nonik0/NONIK0/firmware/rust/src/modes/mod.rs

use crate::{adc::Adc, tone::Tone, Display, Event, SavedSettings, Setting, NUM_CHARS};
use enum_dispatch::enum_dispatch;

#[cfg(feature = "board_v0")]
use avrxmega_hal::{
    port::{mode::*, Pin}
};

#[cfg(feature = "board_v0")]
type ExtPinInt = crate::PB1;

#[cfg(feature = "board_v0")]
pub struct ExtPin(Option<Pin<Input<AnyInput>, ExtPinInt>>);

#[cfg(feature = "board_v0")]
impl ExtPin {
    fn new(
        ext_pin: Pin<Input<AnyInput>, ExtPinInt>,
    ) -> Self {
        Self(Some(ext_pin))
    }

    #[inline(never)]
    fn set_pin_mode(&mut self, pull_up: bool) {
        if let Some(ext_pin) = self.0.take() {
            self.0 = Some(if pull_up {
                ext_pin.into_pull_up_input().forget_imode()
            } else {
                ext_pin.into_floating_input().forget_imode()
            });
        }
    }

    fn to_pull_up(&mut self) {
        self.set_pin_mode(true);
    }

    #[inline(always)]
    fn to_floating(&mut self) {
        self.set_pin_mode(false);
    }
}


mod menu;
#[cfg(not(feature = "no_nametag"))]
mod nametag;
#[cfg(not(feature = "no_i2cutils"))]
mod i2c_utils;
#[cfg(not(feature = "no_random"))]
mod random;
#[cfg(not(feature = "no_sensors"))]
mod sensors;
#[cfg(not(feature = "no_settings"))]
mod settings;
#[cfg(not(feature = "no_traffic"))]
mod traffic;
#[cfg(not(feature = "no_tunnel"))]
mod tunnel;
#[cfg(not(feature = "no_vibes"))]
mod vibes;

pub use menu::*;
#[cfg(not(feature = "no_nametag"))]
pub use nametag::*;
#[cfg(not(feature = "no_i2cutils"))]
pub use i2c_utils::*;
#[cfg(not(feature = "no_random"))]
pub use random::*;
#[cfg(not(feature = "no_sensors"))]
pub use sensors::*;
#[cfg(not(feature = "no_settings"))]
pub use settings::*;
#[cfg(not(feature = "no_traffic"))]
pub use traffic::*;
#[cfg(not(feature = "no_tunnel"))]
pub use tunnel::*;
#[cfg(not(feature = "no_vibes"))]
pub use vibes::*;

pub const NUM_MODES: usize = {
    let mut count = 1;
    #[cfg(not(feature = "no_nametag"))]
    {
        count += 1;
    }
    #[cfg(not(feature = "no_i2cutils"))]
    {
        count += 1;
    }
    #[cfg(not(feature = "no_random"))]
    {
        count += 1;
    }
    #[cfg(not(feature = "no_sensors"))]
    {
        count += 1;
    }
    #[cfg(not(feature = "no_settings"))]
    {
        count += 1;
    }
    #[cfg(not(feature = "no_traffic"))]
    {
        count += 1;
    }
    #[cfg(not(feature = "no_tunnel"))]
    {
        count += 1;
    }
    #[cfg(not(feature = "no_vibes"))]
    {
        count += 1;
    }
    count
};

pub const MODE_NAMES: [&[u8; NUM_CHARS]; NUM_MODES] = [
    b"  NONIK0",
    #[cfg(not(feature = "no_nametag"))]
    b" Nametag",
    #[cfg(not(feature = "no_i2cutils"))]
    b"I2C Util",
    #[cfg(not(feature = "no_random"))]
    b"  Random",
    #[cfg(not(feature = "no_sensors"))]
    b" Sensors",
    #[cfg(not(feature = "no_settings"))]
    b"Settings",
    #[cfg(not(feature = "no_traffic"))]
    b" Traffic",
    #[cfg(not(feature = "no_tunnel"))]
    b"  Tunnel",
    #[cfg(not(feature = "no_vibes"))]
    b"   Vibes",
];

pub struct Context {
    mode_init: bool,
    mode_index: u8,
    pub tone_enabled: bool,
    pub settings: SavedSettings,
}

impl Context {
    pub fn new(settings: SavedSettings) -> Self {
        let mut saved_index = settings.read_setting_byte(Setting::LastMode);
        if saved_index >= NUM_MODES as u8 {
            saved_index = 1;
        }
        Self {
            mode_init: false,
            mode_index: saved_index,
            tone_enabled: settings.read_setting_bool(Setting::Tone),
            settings,
        }
    }

    #[inline(always)]
    pub fn is_menu(&self) -> bool {
        self.mode_index == 0
    }

    #[inline(always)]
    pub fn need_update(&mut self) -> bool {
        let update = !self.mode_init;
        self.mode_init = true;
        update
    }

    #[allow(clippy::wrong_self_convention)]
    pub fn to_menu(&mut self) {
        self.mode_init = false;
        self.mode_index = 0;
    }

    pub fn mode_index(&self) -> usize {
        self.mode_index as usize
    }

    #[allow(clippy::wrong_self_convention)]
    pub fn to_mode(&mut self, index: usize) {
        self.mode_init = false;
        self.mode_index = index as u8;
        self.settings
            .save_setting_byte(Setting::LastMode, self.mode_index);
    }
}

pub struct Peripherals {
    pub adc: Adc,
    pub buzzer: Tone,
    pub display: Display,
    #[cfg(feature = "board_v0")]
    pub ext_pin: ExtPin,
    #[cfg(not(feature = "no_i2cutils"))]
    pub i2c: crate::i2c::I2c,
}

impl Peripherals {
    pub fn new(
        adc: Adc,
        buzzer: Tone,
        display: Display,
        #[cfg(feature = "board_v0")]
        ext_pin: Pin<Input<AnyInput>, ExtPinInt>,
        #[cfg(not(feature = "no_i2cutils"))]
        i2c: crate::i2c::I2c,
    ) -> Self {
        Self {
            adc,
            buzzer,
            display,
            #[cfg(feature = "board_v0")]
            ext_pin: ExtPin::new(ext_pin),
            #[cfg(not(feature = "no_i2cutils"))]
            i2c,
        }
    }
}

#[enum_dispatch]
pub trait ModeHandler {
    fn update(
        &mut self,
        event: &Option<Event>,
        context: &mut Context,
        peripherals: &mut Peripherals,
    );
}

#[enum_dispatch(ModeHandler)]
pub enum Mode {
    Menu(Menu),
    #[cfg(not(feature = "no_nametag"))]
    Nametag(Nametag),
    #[cfg(not(feature = "no_i2cutils"))]
    I2CUtils(I2CUtils),
    #[cfg(not(feature = "no_random"))]
    Random(Random),
    #[cfg(not(feature = "no_sensors"))]
    Sensors(Sensors),
    #[cfg(not(feature = "no_settings"))]
    Settings(Settings),
    #[cfg(not(feature = "no_traffic"))]
    Traffic(Traffic),
    #[cfg(not(feature = "no_tunnel"))]
    Tunnel(Tunnel),
    #[cfg(not(feature = "no_vibes"))]
    Vibes(Vibes),
}

impl Mode {
    pub fn from_context(context: &Context) -> Self {
        let index = context.mode_index();
        let mut i = 0;
        if index == i {
            return Mode::Menu(Menu::new_with_settings(&context.settings));
        }
        i += 1;
        #[cfg(not(feature = "no_nametag"))]
        {
            if index == i {
                return Mode::Nametag(Nametag::new_with_settings(&context.settings));
            }
            i += 1;
        }
        #[cfg(not(feature = "no_i2cutils"))]
        {
            if index == i {
                return Mode::I2CUtils(I2CUtils::new_with_settings(&context.settings));
            }
            i += 1;
        }
        #[cfg(not(feature = "no_random"))]
        {
            if index == i {
                return Mode::Random(Random::new_with_settings(&context.settings));
            }
            i += 1;
        }
        #[cfg(not(feature = "no_sensors"))]
        {
            if index == i {
                return Mode::Sensors(Sensors::new_with_settings(&context.settings));
            }
            i += 1;
        }
        #[cfg(not(feature = "no_settings"))]
        {
            if index == i {
                return Mode::Settings(Settings::new_with_settings(&context.settings));
            }
            i += 1;
        }
        #[cfg(not(feature = "no_traffic"))]
        {
            if index == i {
                return Mode::Traffic(Traffic::new());
            }
            i += 1;
        }
        #[cfg(not(feature = "no_tunnel"))]
        {
            if index == i {
                return Mode::Tunnel(Tunnel::new());
            }
            i += 1;
        }
        #[cfg(not(feature = "no_vibes"))]
        {
            if index == i {
                return Mode::Vibes(Vibes::new());
            }
        }
        panic!("Invalid mode index: {}", index);
    }
}
